happeneddr9/STM32F0-YM2151-VGMPlayer/src/Display/Fonts/RREFonts/rre_arial_62.h

#ifndef __font_Arial62_h__
#define __font_Arial62_h__

#define FONT_CHAR_W 63
#define FONT_CHAR_H 62

const unsigned char fontArial62_Rects[7089] PROGMEM = {
  0x81,0x02,0x83, 0x40,0x6a,0x05, 0x80,0x42,0x45, 0xc1,0xc2,0x03, 0xcc,0xc2,0x03, 0x40,0x82,0x05, 0x05,0x0c,0x00, 0x4b,0x82,0x05, 0x06,0x24,0x00, 0x40,0x5e,0x22, 0x4c,0x84,0x04, 0x52,0xa4,0x04, 0x19,0x84,0x04, 0x05,0xa5,0x04, 0xc9,0x54,0x04, 0x56,0x94,0x03, 
  0x88,0x17,0x42, 0x8d,0x42,0x04, 0x9a,0x42,0x04, 0x84,0x69,0x04, 0x91,0x69,0x04, 0x98,0x08,0x42, 0x95,0x16,0x42, 0x0b,0x49,0x41, 0x57,0x8d,0x04, 0x47,0x9b,0x04, 0x4a,0x8d,0x04, 0x54,0x9b,0x04, 0x92,0x02,0x00, 0x90,0x2d,0x00, 0x5f,0x02,0x00, 0x43,0x2e,0x00, 
  0x1c,0x0d,0x00, 0x40,0x4e,0x22, 0x8e,0x40,0xc2, 0x18,0xdd,0x04, 0x83,0xc7,0x03, 0x86,0x2c,0x12, 0xc8,0x03,0x0e, 0xc2,0x63,0x03, 0xcb,0x17,0x0a, 0x16,0x47,0x04, 0x07,0x54,0x04, 0x92,0x1a,0x08, 0x81,0x4b,0x01, 0x55,0x2a,0x06, 0x44,0x67,0x03, 0x08,0x2f,0x0e, 
  0x46,0x44,0x02, 0xd7,0x46,0x02, 0x96,0x58,0x01, 0x85,0x15,0x08, 0x09,0x2a,0x00, 0x80,0x23,0x01, 0x0b,0x02,0x08, 0x0b,0x30,0x08, 0x1a,0x48,0x01, 0x14,0x44,0x03, 0x03,0x2b,0x08, 0xc2,0x88,0x00, 0x44,0x06,0x07, 0x97,0x67,0x02, 0xc1,0x25,0x05, 0x44,0x51,0x03, 
  0x03,0x22,0x02, 0x09,0x19,0x0f, 0x54,0x1c,0x07, 0x53,0x2b,0x07, 0x05,0x69,0x03, 0x5c,0x0b,0x00, 0x08,0x13,0x01, 0x57,0x1f,0x00, 0x51,0x56,0x00, 0x45,0x45,0x02, 0x93,0x05,0x05, 0x09,0x08,0x00, 0x15,0x09,0x00, 0x16,0x29,0x00, 0x9d,0x60,0x00, 0x81,0xc6,0x03, 
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
  0x068a, 0x0693, 0x06b6, 0x06d2, 0x06f1, 0x070d, 0x072f, 0x0735, 0x075e, 0x076b, 0x076d, 0x0773, 0x0795, 0x0796, 0x07ad, 0x07ba, 
  0x07d8, 0x07f4, 0x0810, 0x081b, 0x083f, 0x0846, 0x0853, 0x086c, 0x0894, 0x08c4, 0x08e7, 0x0900, 0x0915, 0x0916, 0x092b, 0x093b, 
  0x093b, 
};

RRE_Font rre_arial_62 = { RRE_24B, 63,62, 0x20,0x7f, (const uint8_t*)fontArial62_Rects, (const uint16_t*)fontArial62_CharOffs };

#endif
