happeneddr9/STM32F0-YM2151-VGMPlayer/src/Display/Fonts/RREFonts/rre_grot_16x32.h

#ifndef __font_grot_16x32_h__
#define __font_grot_16x32_h__

const unsigned char font_grot_16x32_Rects[3459] PROGMEM = {
  0xc7, 0xc3, 0x02, 0xc7, 0x18, 0x02, 0x43, 0x46, 0x02, 0x49, 0x46, 0x02, 0x05, 0x42, 0x01, 0x0b, 
  0x42, 0x01, 0x44, 0x04, 0x00, 0x4a, 0x04, 0x00, 0x82, 0x09, 0x0d, 0x80, 0x12, 0x0d, 0x88, 0x55, 
  0x01, 0x43, 0x55, 0x01, 0x06, 0x44, 0x01, 0x0a, 0x4c, 0x01, 0xcc, 0x03, 0x01, 0xc5, 0x0c, 0x01, 
  0x8b, 0x46, 0x01, 0x84, 0x4f, 0x01, 0x89, 0x50, 0x01, 0x87, 0x03, 0x01, 0x82, 0x19, 0x01, 0x4e, 
  0x13, 0x00, 0x47, 0x1a, 0x00, 0xc8, 0xc0, 0x40, 0xc3, 0x46, 0x01, 0xcc, 0x50, 0x01, 0x43, 0x18, 
  0x08, 0x86, 0x04, 0x05, 0x45, 0x0e, 0x06, 0x82, 0x16, 0x01, 0x47, 0x0f, 0x05, 0x44, 0x05, 0x08, 
  0xce, 0x12, 0x00, 0x44, 0x0d, 0x03, 0x82, 0x09, 0x00, 0x4c, 0x06, 0x01, 0x07, 0x1a, 0x02, 0x4b, 
  0x17, 0x01, 0x05, 0x07, 0x00, 0x05, 0x0c, 0x00, 0x0b, 0x11, 0x00, 0x04, 0x17, 0x00, 0x42, 0x04, 
  0x04, 0x07, 0x47, 0x01, 0x42, 0x0c, 0x04, 0x49, 0x12, 0x04, 0x07, 0x54, 0x01, 0xc1, 0x45, 0x00, 
  0xce, 0x15, 0x01, 0x49, 0x1a, 0x03, 0x4c, 0x0c, 0x02, 0x48, 0x0e, 0x02, 0x44, 0x10, 0x02, 0x42, 
  0x11, 0x02, 0xc0, 0x07, 0x00, 0x45, 0x05, 0x02, 0x4a, 0x0d, 0x02, 0x46, 0x0f, 0x02, 0x88, 0x18, 
  0x01, 0x03, 0x0e, 0x02, 0x0a, 0x11, 0x02, 0x00, 0x13, 0x02, 0x8d, 0x18, 0x00, 0x4d, 0x13, 0x01, 
  0x02, 0x06, 0x01, 0x0c, 0x19, 0x02, 0x46, 0x0b, 0x01, 0x48, 0x13, 0x01, 0x02, 0x07, 0x00, 0x06, 
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
  0x03c6, 0x03d4, 0x03e2, 0x03ea, 0x03fd, 0x0402, 0x040b, 0x0418, 0x0424, 0x0438, 0x0449, 0x0456, 0x0463, 0x0464, 0x0472, 0x0480, 
};

RRE_Font rre_grot_16x32 = { RRE_NO_SORT|RRE_24B,16,32, 0x20,0x7e, (const uint8_t*)font_grot_16x32_Rects, (const uint16_t*)font_grot_16x32_CharOffs };

#endif
