happeneddr9/STM32F0-YM2151-VGMPlayer/src/Display/Fonts/RREFonts/rre_tahoma_65v.h

#ifndef __font_tahoma77x77_h__
#define __font_tahoma77x77_h__

#define FONT_CHAR_W 71
#define FONT_CHAR_H 65

const unsigned char fontTah65V_Rects[14199] PROGMEM = {
  0x00,0x05,0x0d, 0x00,0x2c,0x07, 0x01,0x05,0x21, 0x01,0x2c,0x07, 0x02,0x05,0x21, 0x02,0x2c,0x07, 0x03,0x05,0x21, 0x03,0x2c,0x07, 0x04,0x05,0x21, 0x04,0x2c,0x07, 0x05,0x05,0x21, 0x05,0x2c,0x07, 0x06,0x05,0x21, 0x06,0x2c,0x07, 0x07,0x05,0x21, 0x07,0x2c,0x07, 
  0x08,0x05,0x21, 0x08,0x2c,0x07, 0x09,0x05,0x21, 0x09,0x2c,0x07, 0x0a,0x05,0x21, 0x0a,0x2c,0x07, 0x0b,0x05,0x0d, 0x0b,0x2c,0x07, 0x00,0x03,0x04, 0x01,0x03,0x0e, 0x02,0x03,0x11, 0x03,0x03,0x11, 0x04,0x03,0x11, 0x05,0x03,0x11, 0x06,0x03,0x11, 0x07,0x03,0x11, 
  0x08,0x03,0x0e, 0x09,0x03,0x04, 0x0d,0x03,0x04, 0x0e,0x03,0x0e, 0x0f,0x03,0x11, 0x10,0x03,0x11, 0x11,0x03,0x11, 0x12,0x03,0x11, 0x13,0x03,0x11, 0x14,0x03,0x11, 0x15,0x03,0x0e, 0x16,0x03,0x04, 0x00,0x22,0x06, 0x01,0x22,0x06, 0x02,0x22,0x06, 0x03,0x10,0x06, 
  0x03,0x22,0x06, 0x04,0x10,0x06, 0x04,0x22,0x06, 0x05,0x10,0x06, 0x05,0x22,0x06, 0x05,0x32,0x01, 0x06,0x10,0x06, 0x06,0x22,0x06, 0x06,0x2e,0x05, 0x07,0x10,0x06, 0x07,0x22,0x06, 0x07,0x2a,0x09, 0x08,0x10,0x06, 0x08,0x22,0x11, 0x09,0x10,0x06, 0x09,0x22,0x11, 
  0x0a,0x10,0x06, 0x0a,0x1f,0x14, 0x0b,0x10,0x06, 0x0b,0x1b,0x18, 0x0c,0x10,0x22, 0x0d,0x10,0x1e, 0x0e,0x0f,0x1b, 0x0f,0x0b,0x1d, 0x10,0x07,0x21, 0x11,0x05,0x19, 0x11,0x22,0x06, 0x12,0x05,0x15, 0x12,0x22,0x06, 0x13,0x05,0x11, 0x13,0x22,0x06, 0x14,0x05,0x11, 
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
  0x0d1d, 0x0d2e, 0x0d6a, 0x0d98, 0x0dcb, 0x0df9, 0x0e3d, 0x0e60, 0x0ea1, 0x0ec2, 0x0ed8, 0x0efc, 0x0f2c, 0x0f37, 0x0f6c, 0x0f8d, 
  0x0fbf, 0x0fed, 0x101b, 0x1033, 0x1075, 0x109a, 0x10bb, 0x10e0, 0x1119, 0x115a, 0x1185, 0x11c2, 0x11f9, 0x1202, 0x1239, 0x1265, 
  0x127d, 
};

RRE_Font rre_tahoma_65v = { RRE_V24B, 71,65, 0x20,0x7f, (const uint8_t*)fontTah65V_Rects, (const uint16_t*)fontTah65V_CharOffs };

#endif
