happeneddr9/STM32F0-YM2151-VGMPlayer/src/Display/GFX_Font.h

/**
 * @Name    : GFX_Font.h
 * @Date    : 2019年11月24日 下午8:05:40
 * @Author  : happe
 * @brief   :
 */

#ifndef DISPLAY_GFX_FONT_H_
#define DISPLAY_GFX_FONT_H_

#include "main.h"

/// Font data stored PER GLYPH
typedef struct {
		uint16_t bitmapOffset;		///< Pointer into GFXfont->bitmap
		uint8_t width;				///< Bitmap dimensions in pixels
		uint8_t height;				///< Bitmap dimensions in pixels
		uint8_t xAdvance;			///< Distance to advance cursor (x axis)
		int8_t xOffset;				///< X dist from cursor pos to UL corner
		int8_t yOffset;				///< Y dist from cursor pos to UL corner
} GFXglyph;

/// Data stored for FONT AS A WHOLE
typedef struct {
		uint8_t *bitmap;			///< Glyph bitmaps, concatenated
		GFXglyph *glyph;			///< Glyph array
		uint8_t first;				///< ASCII extents (first char)
		uint8_t last;				///< ASCII extents (last char)
		uint8_t yAdvance;			///< Newline distance (y axis)
} GFXfont;

// Standard ASCII 5x7 font

static const unsigned char Standard_ASCII_5x7_font[] PROGMEM = {
	0x00, 0x00, 0x00, 0x00, 0x00,				// Offset: 0x00
	0x3E, 0x5B, 0x4F, 0x5B, 0x3E,
	0x3E, 0x6B, 0x4F, 0x6B, 0x3E,
	0x1C, 0x3E, 0x7C, 0x3E, 0x1C,
	0x18, 0x3C, 0x7E, 0x3C, 0x18,				// Offset: 0x04
	0x1C, 0x57, 0x7D, 0x57, 0x1C,
	0x1C, 0x5E, 0x7F, 0x5E, 0x1C,
	0x00, 0x18, 0x3C, 0x18, 0x00,
	0xFF, 0xE7, 0xC3, 0xE7, 0xFF,				// Offset: 0x08
	0x00, 0x18, 0x24, 0x18, 0x00,
	0xFF, 0xE7, 0xDB, 0xE7, 0xFF,
	0x30, 0x48, 0x3A, 0x06, 0x0E,
	0x26, 0x29, 0x79, 0x29, 0x26,				// Offset: 0x0C
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
	0x00, 0x00, 0x00, 0xF0, 0x10,
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
	0xFC, 0x4A, 0x4A, 0x4A, 0x34, 				// sharp-s or beta
	0x7E, 0x02, 0x02, 0x06, 0x06,
	0x02, 0x7E, 0x02, 0x7E, 0x02,
	0x63, 0x55, 0x49, 0x41, 0x63,
	0x38, 0x44, 0x44, 0x3C, 0x04,
	0x40, 0x7E, 0x20, 0x1E, 0x20,
	0x06, 0x02, 0x7E, 0x02, 0x02,
	0x99, 0xA5, 0xE7, 0xA5, 0x99,
	0x1C, 0x2A, 0x49, 0x2A, 0x1C,
	0x4C, 0x72, 0x01, 0x72, 0x4C,
	0x30, 0x4A, 0x4D, 0x4D, 0x30,
	0x30, 0x48, 0x78, 0x48, 0x30,
	0xBC, 0x62, 0x5A, 0x46, 0x3D,
	0x3E, 0x49, 0x49, 0x49, 0x00,
	0x7E, 0x01, 0x01, 0x01, 0x7E,
	0x2A, 0x2A, 0x2A, 0x2A, 0x2A,
	0x44, 0x44, 0x5F, 0x44, 0x44,
	0x40, 0x51, 0x4A, 0x44, 0x40,
	0x40, 0x44, 0x4A, 0x51, 0x40,
	0x00, 0x00, 0xFF, 0x01, 0x03,
	0xE0, 0x80, 0xFF, 0x00, 0x00,
	0x08, 0x08, 0x6B, 0x6B, 0x08,
	0x36, 0x12, 0x36, 0x24, 0x36,
	0x06, 0x0F, 0x09, 0x0F, 0x06,
	0x00, 0x00, 0x18, 0x18, 0x00,
	0x00, 0x00, 0x10, 0x10, 0x00,
	0x30, 0x40, 0xFF, 0x01, 0x01,
	0x00, 0x1F, 0x01, 0x01, 0x1E,
	0x00, 0x19, 0x1D, 0x17, 0x12,
	0x00, 0x3C, 0x3C, 0x3C, 0x3C,
	0x00, 0x00, 0x00, 0x00, 0x00 				// #255 NBSP
};

#endif /* DISPLAY_GFX_FONT_H_ */
