happeneddr9/STM32F0-YM2151-VGMPlayer/src/Display/Fonts/RREFonts/rre_6x8_nosort.h

#ifndef __FONT_6X8_32_127_H__
#define __FONT_6X8_32_127_H__

#define FONT_6X8_32_127_CHAR_WIDTH      6
#define FONT_6X8_32_127_CHAR_HEIGHT     8

const unsigned short font_6x8_Rects[428] PROGMEM = {
  0x4002, 0x0062, 0x1001, 0x1003, 0x4011, 0x4013, 0x0420, 0x0440, 0x6002, 0x0211, 0x0231, 0x0251, 0x0020, 0x0044, 0x0010, 0x0014, 
  0x0023, 0x0032, 0x0041, 0x0050, 0x0054, 0x0102, 0x0122, 0x1040, 0x1043, 0x0161, 0x0011, 0x0014, 0x0031, 0x0034, 0x0064, 0x0002, 
  0x0011, 0x4011, 0x0002, 0x0062, 0x4012, 0x0001, 0x0061, 0x0430, 0x2021, 0x2023, 0x0010, 0x0014, 0x0050, 0x0054, 0x4012, 0x0430, 
  0x0062, 0x0071, 0x0430, 0x0062, 0x0014, 0x0023, 0x0032, 0x0041, 0x0050, 0x4010, 0x4014, 0x0201, 0x0261, 0x0023, 0x0032, 0x0140, 
  0x6002, 0x0261, 0x0011, 0x0460, 0x0201, 0x0231, 0x1014, 0x1040, 0x0010, 0x0201, 0x0261, 0x1014, 0x0132, 0x1044, 0x0010, 0x0050, 
  0x6004, 0x0340, 0x0003, 0x0012, 0x0021, 0x0030, 0x0400, 0x0320, 0x2034, 0x0261, 0x1000, 0x0050, 0x4010, 0x0201, 0x0330, 0x0261, 
  0x1044, 0x0014, 0x0400, 0x2004, 0x1033, 0x1052, 0x0201, 0x0231, 0x0261, 0x1010, 0x1014, 0x1040, 0x1044, 0x4014, 0x0201, 0x0231, 
  0x0261, 0x1010, 0x0050, 0x0032, 0x0062, 0x0032, 0x0062, 0x0071, 0x0003, 0x0012, 0x0021, 0x0030, 0x0041, 0x0052, 0x0063, 0x0420, 
  0x0440, 0x0000, 0x0011, 0x0022, 0x0033, 0x0042, 0x0051, 0x0060, 0x0201, 0x1014, 0x0010, 0x0033, 0x0042, 0x0062, 0x1232, 0x4010, 
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
  0x0161, 0x0165, 0x0169, 0x016c, 0x0171, 0x0174, 0x0177, 0x017c, 0x0181, 0x018a, 0x018e, 0x0193, 0x0198, 0x0199, 0x019e, 0x01a2, 
  0x01a2, 
};

RRE_Font rre_6x8 = { RRE_NO_SORT, 6,8, 0x20,0x7f, (const uint8_t*)font_6x8_Rects, (const uint16_t*)font_6x8_CharOffs };

#endif 
