happeneddr9/STM32F0-YM2151-VGMPlayer/src/Display/Fonts/RREFonts/rre_7x8_nosort.h

#ifndef __FONT_7X8_32_127_H__
#define __FONT_7X8_32_127_H__

#define FONT_7X8_32_127_CHAR_WIDTH      7 
#define FONT_7X8_32_127_CHAR_HEIGHT     8

const unsigned short font_7x8_Rects[428] PROGMEM = {
  0x4003, 0x0063, 0x1002, 0x1004, 0x4012, 0x4014, 0x0421, 0x0441, 0x0311, 0x0331, 0x0351, 0x0003, 0x0020, 0x0045, 0x1053, 0x0000, 
  0x0005, 0x0014, 0x0023, 0x0032, 0x0041, 0x0050, 0x0055, 0x0202, 0x0222, 0x0261, 0x1040, 0x1044, 0x0011, 0x0015, 0x0031, 0x0035, 
  0x0065, 0x0003, 0x0012, 0x4012, 0x0003, 0x0063, 0x4013, 0x0002, 0x0062, 0x0431, 0x2022, 0x2024, 0x0011, 0x0015, 0x0051, 0x0055, 
  0x4013, 0x0431, 0x0063, 0x0072, 0x0431, 0x0063, 0x0015, 0x0024, 0x0033, 0x0042, 0x0051, 0x0060, 0x4010, 0x4015, 0x0301, 0x0361, 
  0x1004, 0x0023, 0x0032, 0x0140, 0x6002, 0x0460, 0x0011, 0x0560, 0x0301, 0x0331, 0x1015, 0x1040, 0x0010, 0x0301, 0x0361, 0x1015, 
  0x0133, 0x1045, 0x0010, 0x0050, 0x6004, 0x0540, 0x0003, 0x0012, 0x0021, 0x0030, 0x0500, 0x0420, 0x0361, 0x2035, 0x1000, 0x0050, 
  0x4010, 0x0301, 0x0430, 0x0361, 0x1045, 0x0015, 0x0500, 0x2005, 0x1034, 0x1053, 0x0301, 0x0331, 0x0361, 0x1010, 0x1015, 0x1040, 
  0x1045, 0x4015, 0x0301, 0x0331, 0x0361, 0x1010, 0x0050, 0x0033, 0x0063, 0x0033, 0x0063, 0x0072, 0x0004, 0x0013, 0x0022, 0x0031, 
  0x0042, 0x0053, 0x0064, 0x0421, 0x0441, 0x0001, 0x0012, 0x0023, 0x0034, 0x0043, 0x0052, 0x0061, 0x0301, 0x1015, 0x0010, 0x0034, 
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
  0x016b, 0x016f, 0x0173, 0x0176, 0x017b, 0x017e, 0x0181, 0x0186, 0x018b, 0x0194, 0x0198, 0x019d, 0x01a2, 0x01a3, 0x01a8, 0x01ac, 
};

RRE_Font rre_7x8 = { RRE_NO_SORT, 7,8, 0x20,0x7e, (const uint8_t*)font_7x8_Rects, (const uint16_t*)font_7x8_CharOffs };

#endif 
